ArielWolle/McMaster_Project_4/CAD/Autodesk Inventor/Mon-46 Controller/BaseEnd-Powered.STL

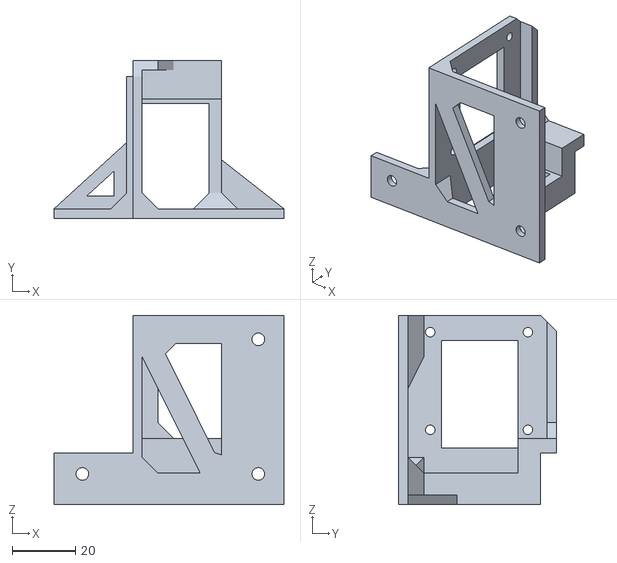
[picture p42: CAD file, 2021-04-01]
CAD/Autodesk Inventor/Mon-46 Controller/BaseEnd-Powered.STL
73.0 x 50.0 x 60.0
