ArielWolle/McMaster_Project_4/CAD/Autodesk Inventor/Mon-46 Controller/PenSlider.STL

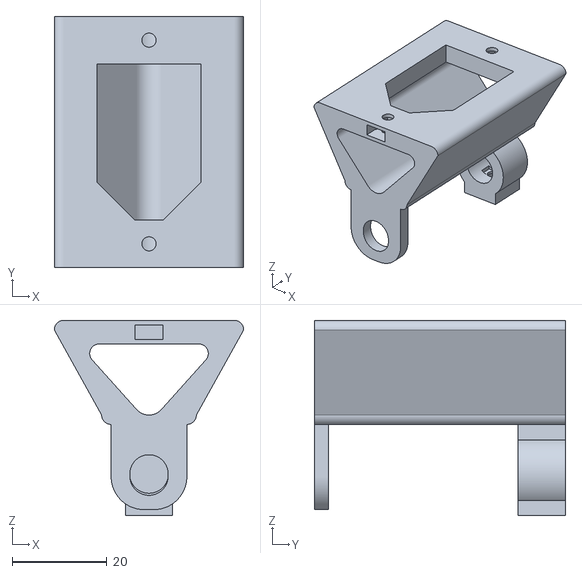
[picture p43: CAD file, 2021-04-01]
CAD/Autodesk Inventor/Mon-46 Controller/PenSlider.STL
40.0 x 53.0 x 41.2
